ParksDevelopment/BlueShell/BlueShell/PCB/blueShell.kicad_sch

## KiCad design BlueShell/PCB/blueShell.kicad_sch (2024-05-05)

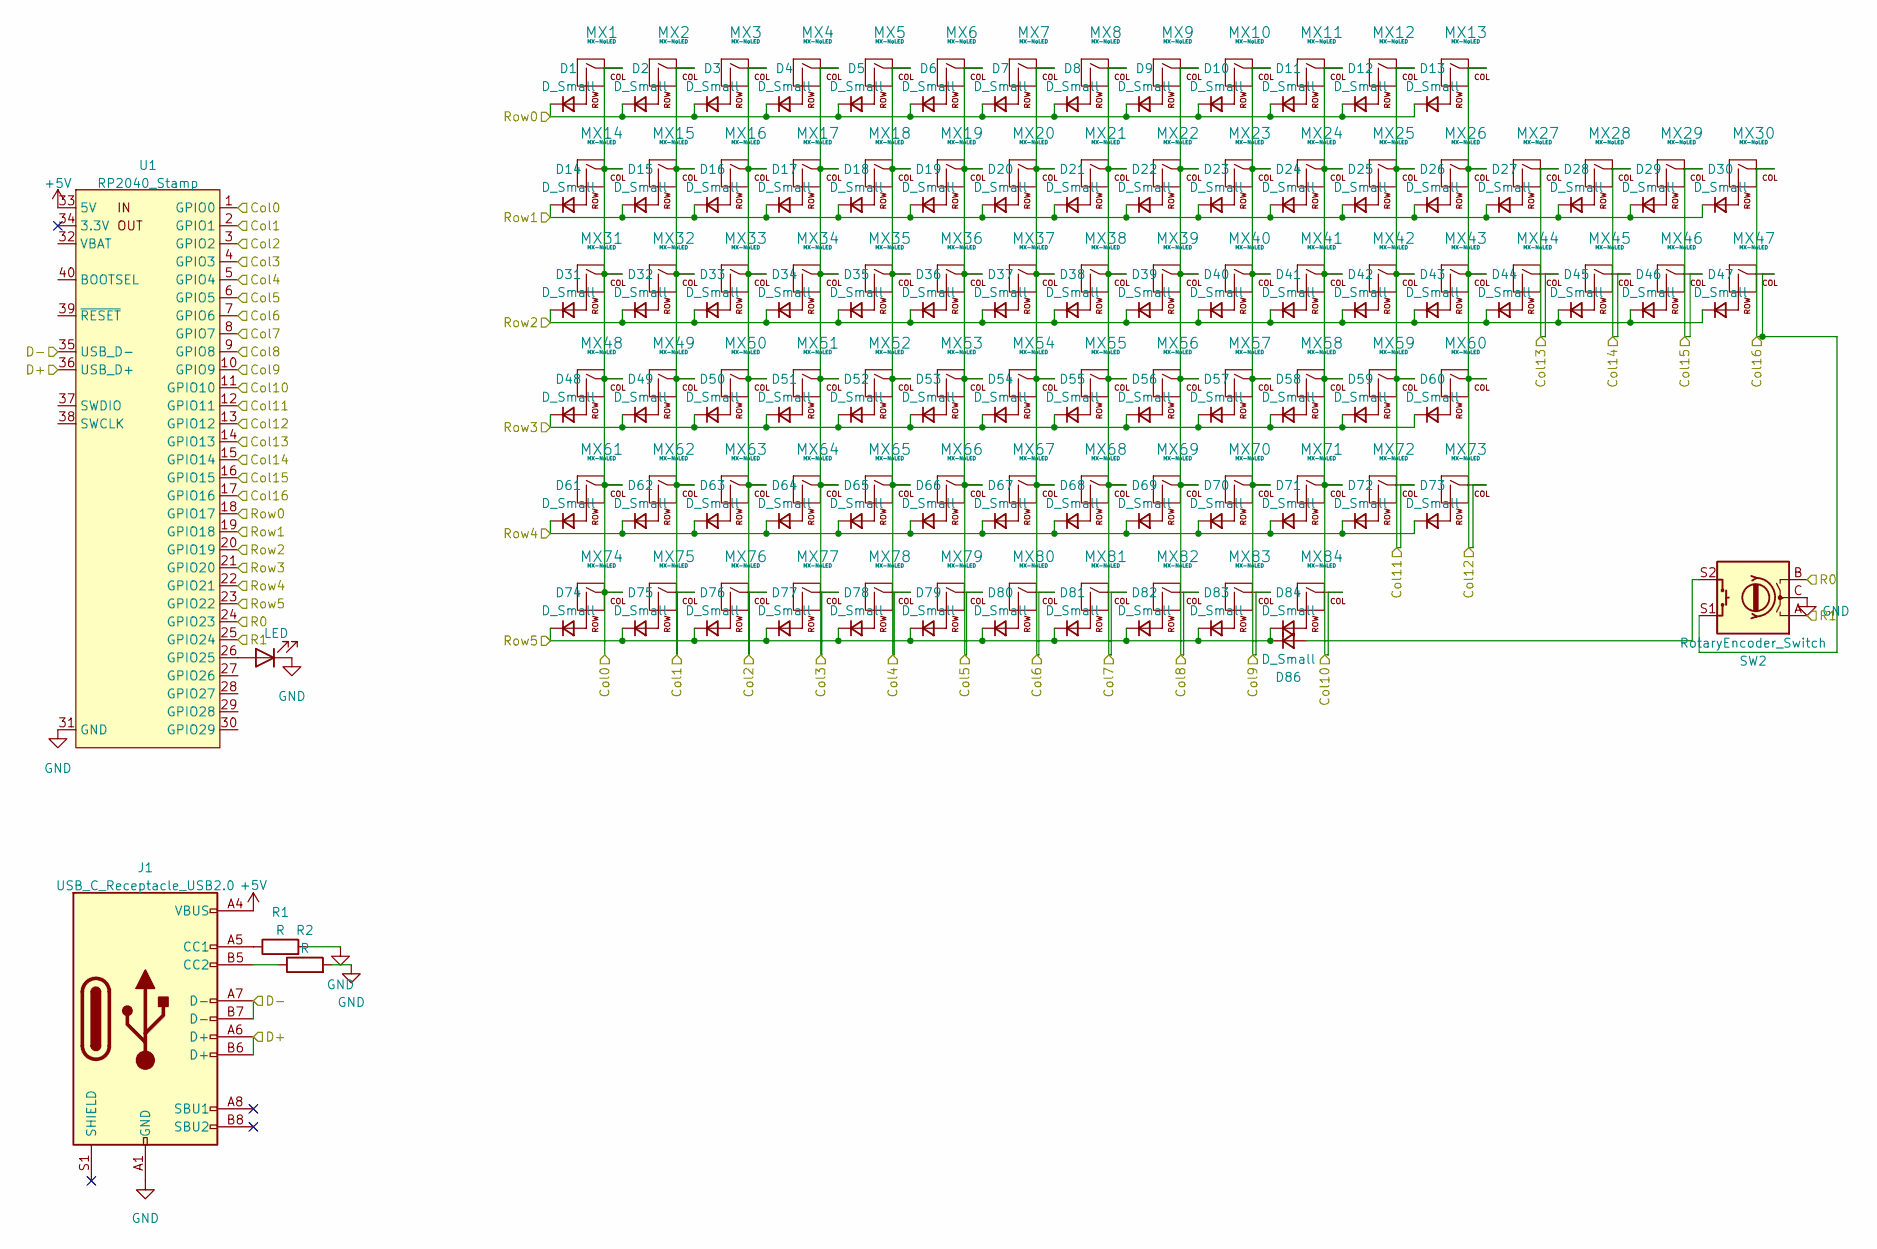
[picture p17: schematic blueShell.kicad_sch]

Parts:
D1, D2, D3, D4, D5, D6, D7, D8, D9, D10, D11, D12, D13, D14, D15, D16, D17, D18, D19, D20, D21, D22, D23, D24, D25, D26, D27, D28, D29, D30, D31, D32, D33, D34, D35, D36, D37, D38, D39, D40, D41, D42, D43, D44, D45, D46, D47, D48, D49, D50, D51, D52, D53, D54, D55, D56, D57, D58, D59, D60, D61, D62, D63, D64, D65, D66, D67, D68, D69, D70, D71, D72, D73, D74, D75, D76, D77, D78, D79, D80, D81, D82, D83, D84, D86: D_Small; Diode
D85: LED; LED_3mm
J1: USB_C_Receptacle_USB2.0; USB_C_Receptacle_HRO_TYPE-C-31-M-12
MX1, MX2, MX3, MX4, MX5, MX6, MX7, MX8, MX9, MX10, MX11, MX12, MX13, MX14, MX15, MX16, MX17, MX18, MX19, MX20, MX21, MX22, MX23, MX24, MX25, MX26, MX28, MX29, MX30, MX32, MX33, MX34, MX35, MX36, MX37, MX38, MX39, MX40, MX41, MX42, MX43, MX45, MX46, MX47, MX49, MX50, MX51, MX52, MX53, MX54, MX55, MX56, MX57, MX58, MX59, MX62, MX63, MX64, MX65, MX66, MX67, MX68, MX69, MX70, MX71, MX73, MX82, MX83, MX84: MX-NoLED; MX-Hotswap-1U
MX27: MX-NoLED; MX-Hotswap-2U
MX31, MX44: MX-NoLED; MX-Hotswap-1.5U
MX48: MX-NoLED; MX-Hotswap-1.75U
MX60, MX61: MX-NoLED; MX-Hotswap-2.25U
MX72: MX-NoLED; MX-Hotswap-2.75U
MX74, MX75, MX76, MX78, MX79, MX80, MX81: MX-NoLED; MX-Hotswap-1.25U
MX77: MX-NoLED; MX-Hotswap-6.25U
R1, R2: R; Resistor
SW2: RotaryEncoder_Switch; RotaryEncoder_Alps_EC11E-Switch_Vertical_H20mm
U1: RP2040_Stamp; RP2040_Stamp_THT

Connections:
+5V: J1.A4 (VBUS), J1.A9 (VBUS), J1.B4 (VBUS), J1.B9 (VBUS), U1.33 (5V)
Col0: MX1.1 (COL), MX14.1 (COL), MX31.1 (COL), MX48.1 (COL), MX61.1 (COL), MX74.1 (COL), U1.1 (GPIO0)
Col1: MX2.1 (COL), MX15.1 (COL), MX32.1 (COL), MX49.1 (COL), MX62.1 (COL), MX75.1 (COL), U1.2 (GPIO1)
Col2: MX3.1 (COL), MX16.1 (COL), MX33.1 (COL), MX50.1 (COL), MX63.1 (COL), MX76.1 (COL), U1.3 (GPIO2)
Col3: MX4.1 (COL), MX17.1 (COL), MX34.1 (COL), MX51.1 (COL), MX64.1 (COL), MX77.1 (COL), U1.4 (GPIO3)
Col4: MX5.1 (COL), MX18.1 (COL), MX35.1 (COL), MX52.1 (COL), MX65.1 (COL), MX78.1 (COL), U1.5 (GPIO4)
Col5: MX6.1 (COL), MX19.1 (COL), MX36.1 (COL), MX53.1 (COL), MX66.1 (COL), MX79.1 (COL), U1.6 (GPIO5)
Col6: MX7.1 (COL), MX20.1 (COL), MX37.1 (COL), MX54.1 (COL), MX67.1 (COL), MX80.1 (COL), U1.7 (GPIO6)
Col7: MX8.1 (COL), MX21.1 (COL), MX38.1 (COL), MX55.1 (COL), MX68.1 (COL), MX81.1 (COL), U1.8 (GPIO7)
Col8: MX9.1 (COL), MX22.1 (COL), MX39.1 (COL), MX56.1 (COL), MX69.1 (COL), MX82.1 (COL), U1.9 (GPIO8)
Col9: MX10.1 (COL), MX23.1 (COL), MX40.1 (COL), MX57.1 (COL), MX70.1 (COL), MX83.1 (COL), U1.10 (GPIO9)
Col10: MX11.1 (COL), MX24.1 (COL), MX41.1 (COL), MX58.1 (COL), MX71.1 (COL), MX84.1 (COL), U1.11 (GPIO10)
Col11: MX12.1 (COL), MX25.1 (COL), MX42.1 (COL), MX59.1 (COL), MX72.1 (COL), U1.12 (GPIO11)
Col12: MX13.1 (COL), MX26.1 (COL), MX43.1 (COL), MX60.1 (COL), MX73.1 (COL), U1.13 (GPIO12)
Col13: MX27.1 (COL), MX44.1 (COL), U1.14 (GPIO13)
Col14: MX28.1 (COL), MX45.1 (COL), U1.15 (GPIO14)
Col15: MX29.1 (COL), MX46.1 (COL), U1.16 (GPIO15)
Col16: MX30.1 (COL), MX47.1 (COL), SW2.S1, U1.17 (GPIO16)
D+: J1.A6 (D+), J1.B6 (D+), U1.36 (USB_D+)
D-: J1.A7 (D-), J1.B7 (D-), U1.35 (USB_D-)
GND: D85.1 (K), J1.A1 (GND), J1.A12 (GND), J1.B1 (GND), J1.B12 (GND), R1.2, R2.2, SW2.C, U1.31 (GND)
unnamed: D1.2 (A), MX1.2 (ROW)
unnamed: D2.2 (A), MX2.2 (ROW)
unnamed: D3.2 (A), MX3.2 (ROW)
unnamed: D4.2 (A), MX4.2 (ROW)
unnamed: D5.2 (A), MX5.2 (ROW)
unnamed: D6.2 (A), MX6.2 (ROW)
unnamed: D7.2 (A), MX7.2 (ROW)
unnamed: D8.2 (A), MX8.2 (ROW)
unnamed: D9.2 (A), MX9.2 (ROW)
unnamed: D10.2 (A), MX10.2 (ROW)
unnamed: D11.2 (A), MX11.2 (ROW)
unnamed: D12.2 (A), MX12.2 (ROW)
unnamed: D13.2 (A), MX13.2 (ROW)
unnamed: D14.2 (A), MX14.2 (ROW)
unnamed: D15.2 (A), MX15.2 (ROW)
unnamed: D16.2 (A), MX16.2 (ROW)
unnamed: D17.2 (A), MX17.2 (ROW)
unnamed: D18.2 (A), MX18.2 (ROW)
unnamed: D19.2 (A), MX19.2 (ROW)
unnamed: D20.2 (A), MX20.2 (ROW)
unnamed: D21.2 (A), MX21.2 (ROW)
unnamed: D22.2 (A), MX22.2 (ROW)
unnamed: D23.2 (A), MX23.2 (ROW)
unnamed: D24.2 (A), MX24.2 (ROW)
unnamed: D25.2 (A), MX25.2 (ROW)
unnamed: D26.2 (A), MX26.2 (ROW)
unnamed: D27.2 (A), MX27.2 (ROW)
unnamed: D28.2 (A), MX28.2 (ROW)
unnamed: D29.2 (A), MX29.2 (ROW)
unnamed: D30.2 (A), MX30.2 (ROW)
unnamed: D31.2 (A), MX31.2 (ROW)
unnamed: D32.2 (A), MX32.2 (ROW)
unnamed: D33.2 (A), MX33.2 (ROW)
unnamed: D34.2 (A), MX34.2 (ROW)
unnamed: D35.2 (A), MX35.2 (ROW)
unnamed: D36.2 (A), MX36.2 (ROW)
unnamed: D37.2 (A), MX37.2 (ROW)
unnamed: D38.2 (A), MX38.2 (ROW)
unnamed: D39.2 (A), MX39.2 (ROW)
unnamed: D40.2 (A), MX40.2 (ROW)
unnamed: D41.2 (A), MX41.2 (ROW)
unnamed: D42.2 (A), MX42.2 (ROW)
unnamed: D43.2 (A), MX43.2 (ROW)
unnamed: D44.2 (A), MX44.2 (ROW)
unnamed: D45.2 (A), MX45.2 (ROW)
unnamed: D46.2 (A), MX46.2 (ROW)
unnamed: D47.2 (A), MX47.2 (ROW)
unnamed: D48.2 (A), MX48.2 (ROW)
unnamed: D49.2 (A), MX49.2 (ROW)
unnamed: D50.2 (A), MX50.2 (ROW)
unnamed: D51.2 (A), MX51.2 (ROW)
unnamed: D52.2 (A), MX52.2 (ROW)
unnamed: D53.2 (A), MX53.2 (ROW)
unnamed: D54.2 (A), MX54.2 (ROW)
unnamed: D55.2 (A), MX55.2 (ROW)
unnamed: D56.2 (A), MX56.2 (ROW)
unnamed: D57.2 (A), MX57.2 (ROW)
unnamed: D58.2 (A), MX58.2 (ROW)
unnamed: D59.2 (A), MX59.2 (ROW)
unnamed: D60.2 (A), MX60.2 (ROW)
unnamed: D61.2 (A), MX61.2 (ROW)
unnamed: D62.2 (A), MX62.2 (ROW)
unnamed: D63.2 (A), MX63.2 (ROW)
unnamed: D64.2 (A), MX64.2 (ROW)
unnamed: D65.2 (A), MX65.2 (ROW)
unnamed: D66.2 (A), MX66.2 (ROW)
unnamed: D67.2 (A), MX67.2 (ROW)
unnamed: D68.2 (A), MX68.2 (ROW)
unnamed: D69.2 (A), MX69.2 (ROW)
unnamed: D70.2 (A), MX70.2 (ROW)
unnamed: D71.2 (A), MX71.2 (ROW)
unnamed: D72.2 (A), MX72.2 (ROW)
unnamed: D73.2 (A), MX73.2 (ROW)
unnamed: D74.2 (A), MX74.2 (ROW)
unnamed: D75.2 (A), MX75.2 (ROW)
unnamed: D76.2 (A), MX76.2 (ROW)
unnamed: D77.2 (A), MX77.2 (ROW)
unnamed: D78.2 (A), MX78.2 (ROW)
unnamed: D79.2 (A), MX79.2 (ROW)
unnamed: D80.2 (A), MX80.2 (ROW)
unnamed: D81.2 (A), MX81.2 (ROW)
unnamed: D82.2 (A), MX82.2 (ROW)
unnamed: D83.2 (A), MX83.2 (ROW)
unnamed: D84.2 (A), MX84.2 (ROW)
unnamed: D85.2 (A), U1.26 (GPIO25)
unnamed: D86.2 (A), SW2.S2
unnamed: J1.A5 (CC1), R1.1
unnamed: J1.B5 (CC2), R2.1
R0: SW2.B, U1.24 (GPIO23)
R1: SW2.A, U1.25 (GPIO24)
Row0: D1.1 (K), D2.1 (K), D3.1 (K), D4.1 (K), D5.1 (K), D6.1 (K), D7.1 (K), D8.1 (K), D9.1 (K), D10.1 (K), D11.1 (K), D12.1 (K), D13.1 (K), U1.18 (GPIO17)
Row1: D14.1 (K), D15.1 (K), D16.1 (K), D17.1 (K), D18.1 (K), D19.1 (K), D20.1 (K), D21.1 (K), D22.1 (K), D23.1 (K), D24.1 (K), D25.1 (K), D26.1 (K), D27.1 (K), D28.1 (K), D29.1 (K), D30.1 (K), U1.19 (GPIO18)
Row2: D31.1 (K), D32.1 (K), D33.1 (K), D34.1 (K), D35.1 (K), D36.1 (K), D37.1 (K), D38.1 (K), D39.1 (K), D40.1 (K), D41.1 (K), D42.1 (K), D43.1 (K), D44.1 (K), D45.1 (K), D46.1 (K), D47.1 (K), U1.20 (GPIO19)
Row3: D48.1 (K), D49.1 (K), D50.1 (K), D51.1 (K), D52.1 (K), D53.1 (K), D54.1 (K), D55.1 (K), D56.1 (K), D57.1 (K), D58.1 (K), D59.1 (K), D60.1 (K), U1.21 (GPIO20)
Row4: D61.1 (K), D62.1 (K), D63.1 (K), D64.1 (K), D65.1 (K), D66.1 (K), D67.1 (K), D68.1 (K), D69.1 (K), D70.1 (K), D71.1 (K), D72.1 (K), D73.1 (K), U1.22 (GPIO21)
Row5: D74.1 (K), D75.1 (K), D76.1 (K), D77.1 (K), D78.1 (K), D79.1 (K), D80.1 (K), D81.1 (K), D82.1 (K), D83.1 (K), D84.1 (K), D86.1 (K), U1.23 (GPIO22)
